MorganTA/cosplay-prop---BotW-bomb/Assembly Pictures/BoTW Remote Bomb Assembly (2).jpg

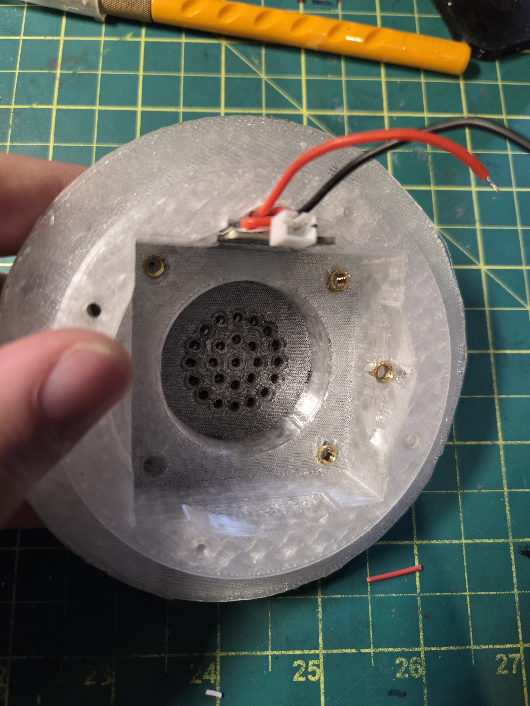
Assembly Pictures/BoTW Remote Bomb Assembly (2).jpg
