MorganTA/cosplay-prop---BotW-bomb/Assembly Pictures/BoTW Remote Bomb Assembly (3).jpg

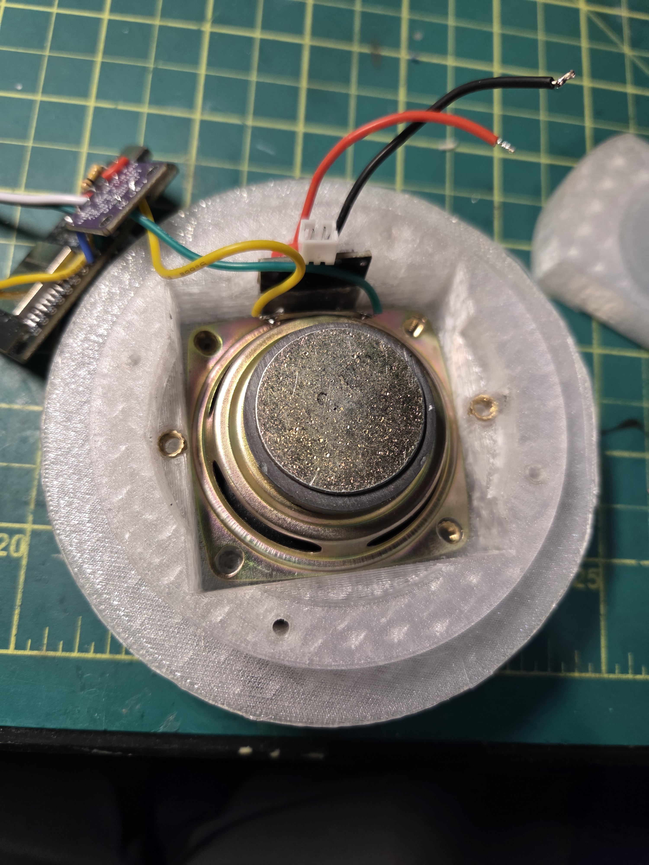
Assembly Pictures/BoTW Remote Bomb Assembly (3).jpg
