MorganTA/cosplay-prop---BotW-bomb/Assembly Pictures/BoTW Remote Bomb Assembly (6).jpg

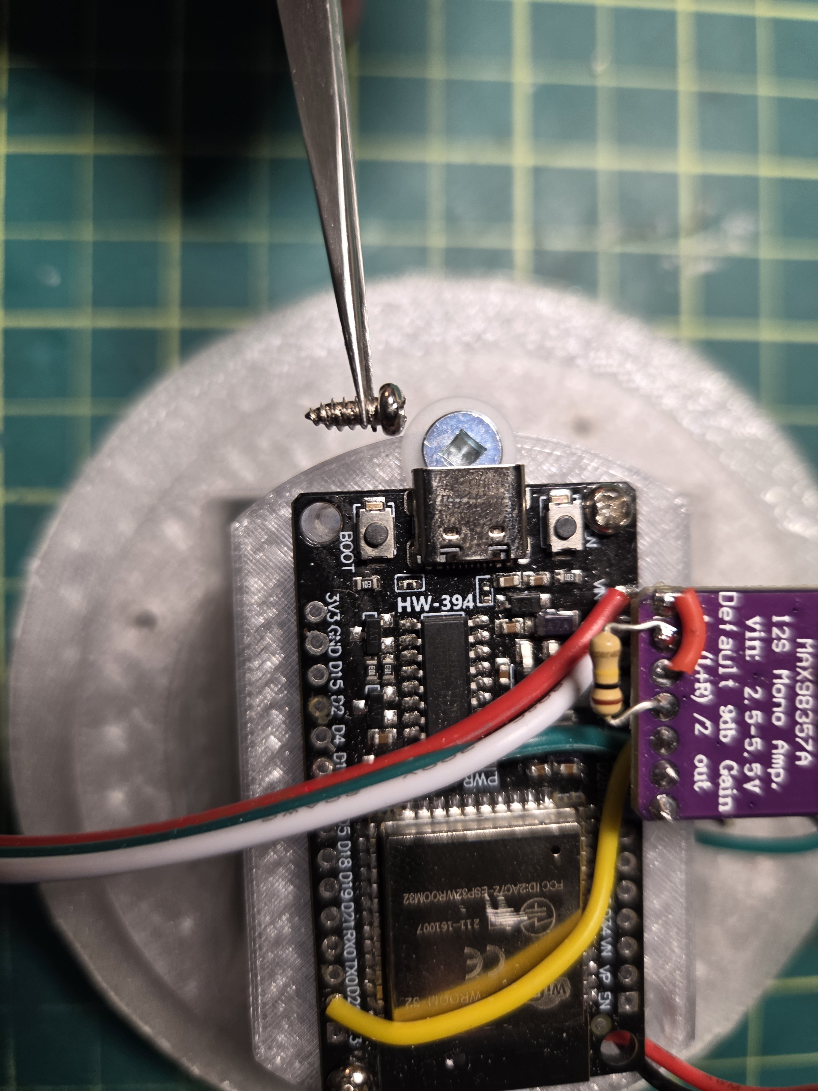
Assembly Pictures/BoTW Remote Bomb Assembly (6).jpg
