MorganTA/cosplay-prop---BotW-bomb/Assembly Pictures/BoTW Remote Bomb Assembly (7).jpg

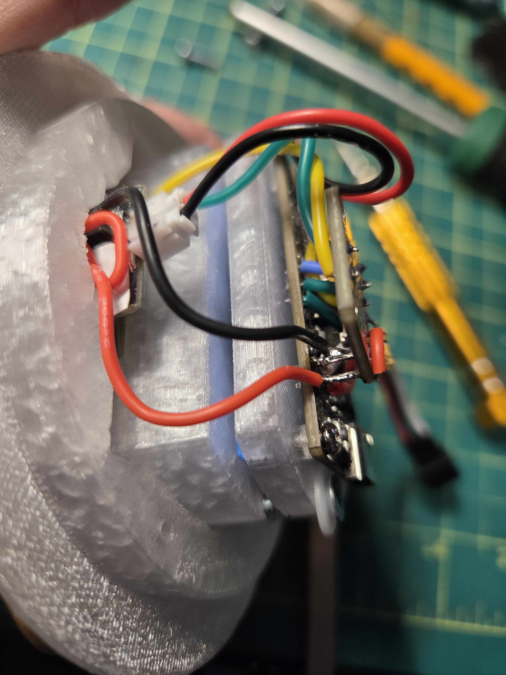
Assembly Pictures/BoTW Remote Bomb Assembly (7).jpg
