MorganTA/cosplay-prop---BotW-bomb/Assembly Pictures/BoTW Remote Bomb Assembly (1).jpg

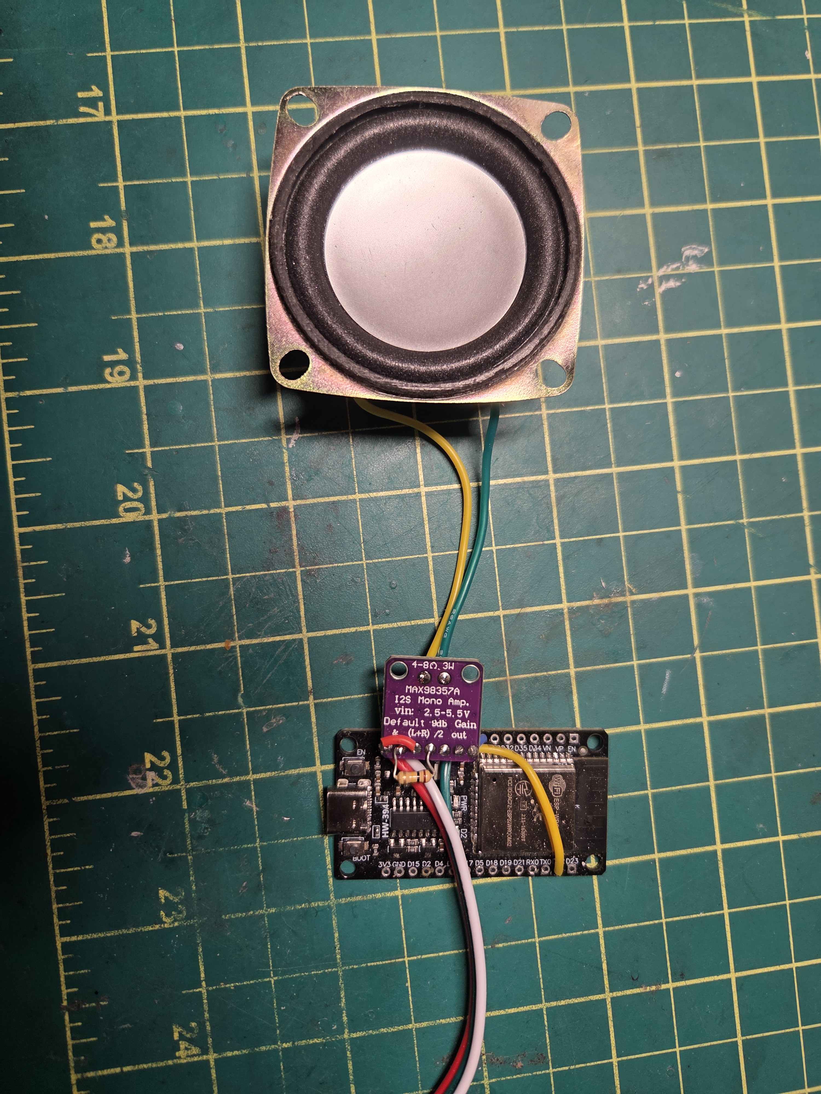
Assembly Pictures/BoTW Remote Bomb Assembly (1).jpg
